DustinWatts/esp32-touchdown/Images/ESP32_TouchDown_3.jpg

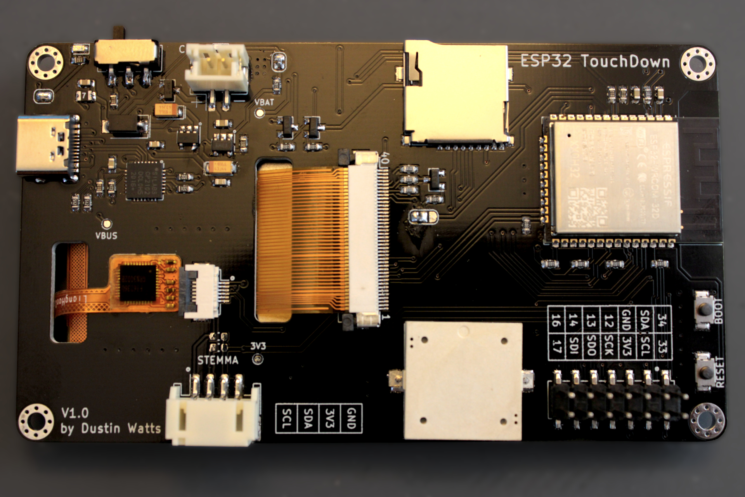
Images/ESP32_TouchDown_3.jpg
