DustinWatts/esp32-touchdown/Images/ESP32_TouchDown_features.png

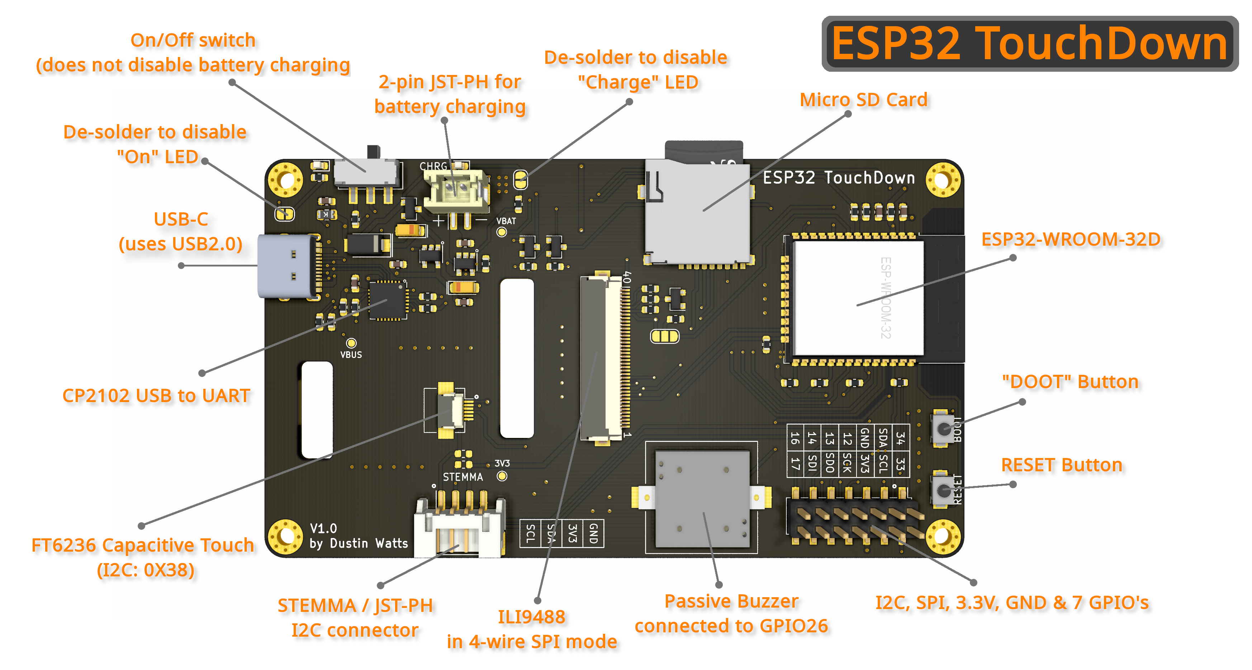
Images/ESP32_TouchDown_features.png
