DustinWatts/esp32-touchdown/Examples/ESP32_TouchDown_Test/data/thumbsup.bmp

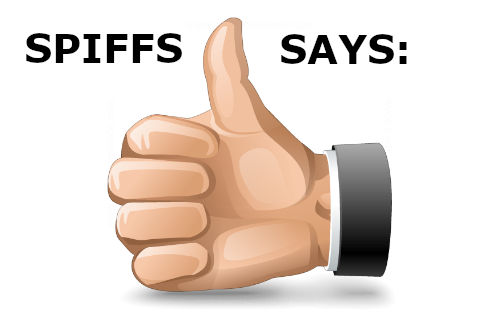
Examples/ESP32_TouchDown_Test/data/thumbsup.bmp
