DustinWatts/esp32-touchdown/Examples/ESP32_TouchDown_Test/sd card/thumbsup.bmp

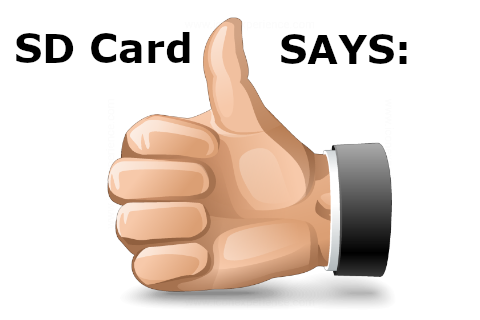
Examples/ESP32_TouchDown_Test/sd card/thumbsup.bmp
